nanovna-v2/NanoVNA2/fab/v2_0-20190924_08_28/v2_0-20190924_08_28-bottom.png

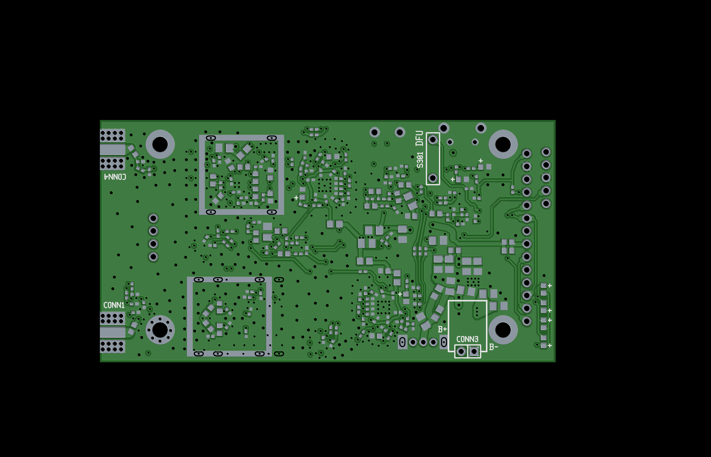
fab/v2_0-20190924_08_28/v2_0-20190924_08_28-bottom.png
